m-lima/nantor/case/freecad/sources/v2/inner_bounds.dxf

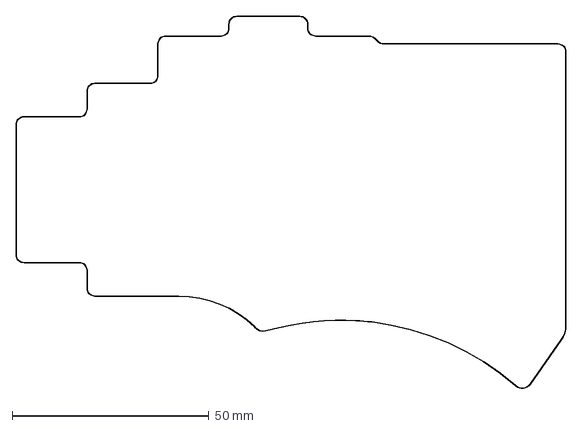
[picture p17: CAD file, 2025-08-29]
case/freecad/sources/v2/inner_bounds.dxf
139.5 x 94.5 mm
