m-lima/nantor/case/fusion/sources/hex.dxf

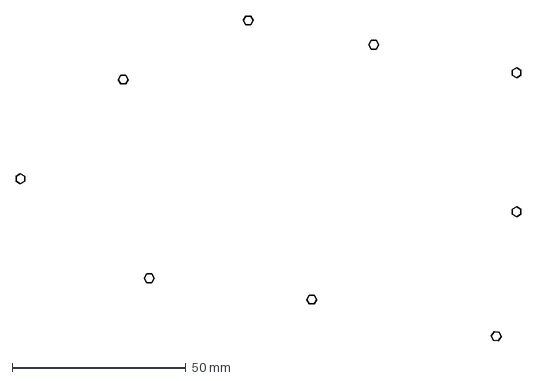
[picture p18: CAD file, 2025-08-29]
case/fusion/sources/hex.dxf
145.1 x 93.4 mm
