m-lima/nantor/case/freecad/sources/v2/feet_tolerance.dxf

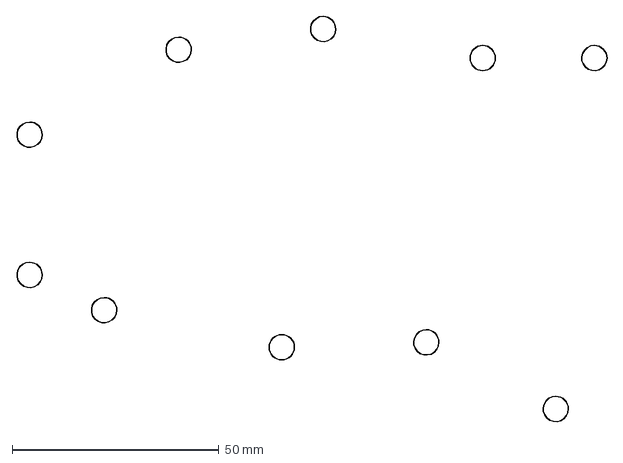
[picture p19: CAD file, 2025-08-29]
case/freecad/sources/v2/feet_tolerance.dxf
142.8 x 98.1 mm
