m-lima/nantor/case/fusion/sources/wall_holes_bottom.dxf

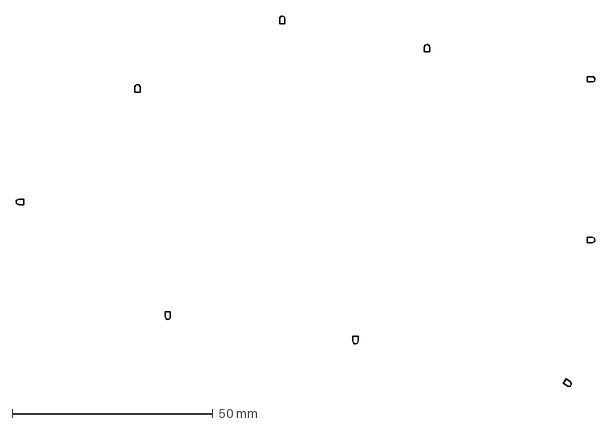
[picture p20: CAD file, 2025-08-29]
case/fusion/sources/wall_holes_bottom.dxf
143.9 x 92.2 mm
