m-lima/nantor/case/fusion/sources/case_top.dxf

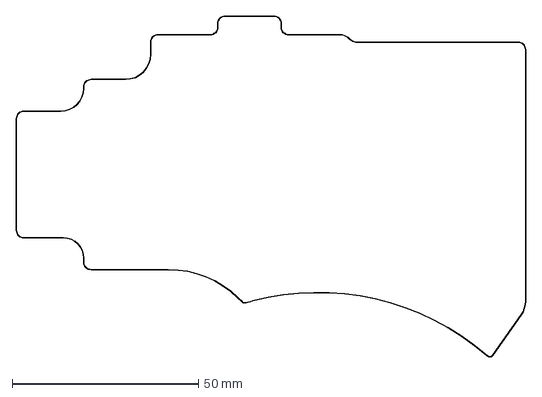
[picture p22: CAD file, 2025-08-29]
case/fusion/sources/case_top.dxf
136.5 x 91.4 mm
