m-lima/nantor/case/freecad/sources/v2/inner_bounds_tolerance.dxf

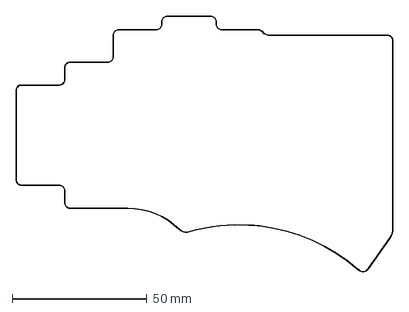
[picture p23: CAD file, 2025-08-29]
case/freecad/sources/v2/inner_bounds_tolerance.dxf
139.7 x 94.7 mm
