m-lima/nantor/case/fusion/sources/wells_bottom.dxf

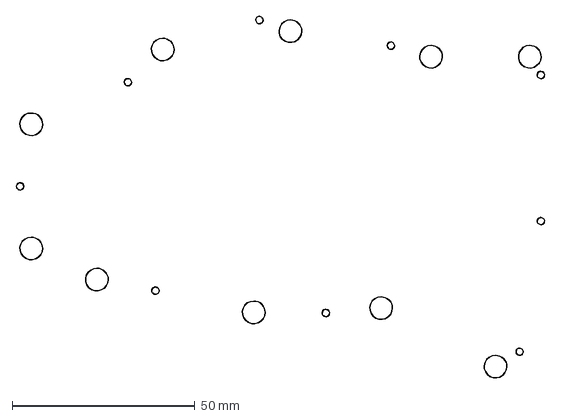
[picture p24: CAD file, 2025-08-29]
case/fusion/sources/wells_bottom.dxf
144.8 x 99.3 mm
