m-lima/nantor/case/freecad/sources/v2/bounds.dxf

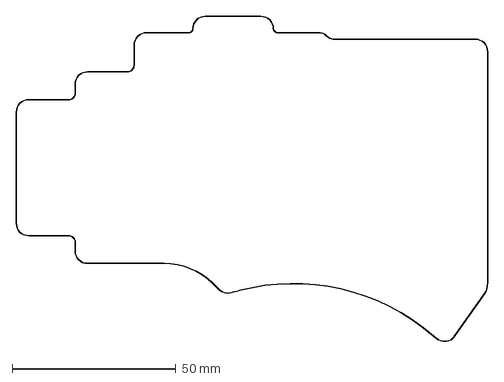
[picture p25: CAD file, 2025-08-29]
case/freecad/sources/v2/bounds.dxf
144.1 x 99.5 mm
