m-lima/nantor/case/freecad/sources/v2/wells_left.dxf

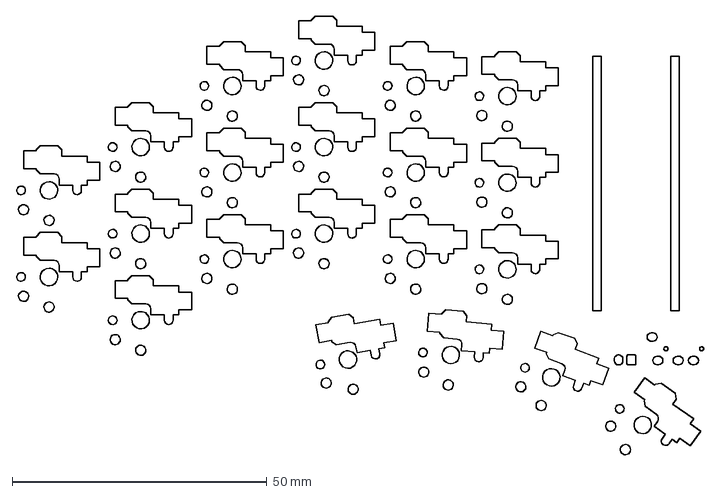
[picture p26: CAD file, 2025-08-29]
case/freecad/sources/v2/wells_left.dxf
135.0 x 86.2 mm
