m-lima/nantor/case/freecad/sources/v2/nantor.stl

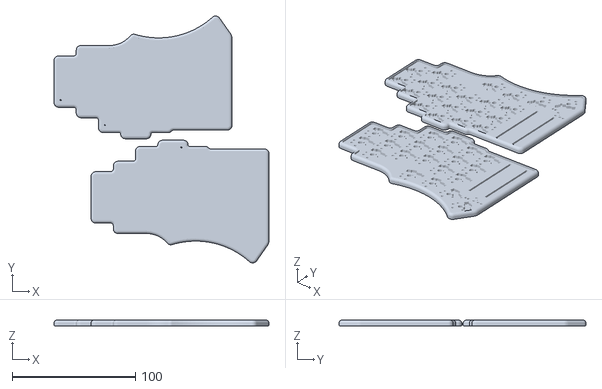
[picture p27: CAD file, 2025-08-29]
case/freecad/sources/v2/nantor.stl
174.1 x 200.0 x 4.60
